Egokitek/Tinycorder/SRC/Badges.cpp

///////////////////////////////////////////////////////////
///                  TINYCORDER V2.0                    ///
///////////////////////////////////////////////////////////
///                    MAIN PROGRAM                     ///
///////////////////////////////////////////////////////////
///           Victor Barahona - July 2025               ///
///                www.victorbarahona.com               ///
///////////////////////////////////////////////////////////

#include "Badges.h"

/*
*****************************************************************************************************
***                                 HOW TO CREATE OTHER BADGES                                    ***
*** Create a jpg file with 400x240pixels. Could be made in www.canva.com with a customized canvas ***
***                                 Download the jpg file to PC.                                  ***
***              Open https://javl.github.io/image2cpp/ an insert the jpg file.                   ***
***        Follow the wizard and you will obtain the code to insert in your Tinycorder            ***
*****************************************************************************************************
*/

//Badge personal Victor Barahona asociado a www.victorbarahona.com
const unsigned char vj_personal_badge[] PROGMEM = {
  // 'Badge personal Victor Barahona, 400x240px
  0xff, 0xff, 0xff, 0xff, 0xff, 0xff, 0xff, 0xff, 0xff, 0xff, 0xff, 0xff, 0xff, 0xff, 0xff, 0xff,
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
  0xff, 0xff, 0xff, 0xff, 0xff, 0xff, 0xff, 0xff, 0xff, 0xff, 0xff, 0xff, 0xff, 0x00, 0x00, 0x3f,
  0xff, 0xff, 0xff, 0xff, 0xff, 0xff, 0xff, 0xff, 0xff, 0xfc, 0x07, 0xff, 0xff, 0xff, 0xff, 0xff,
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
};


//////////////////////
///   END OF FILE  ///
//////////////////////
