Egokitek/Tinycorder/SRC/Badges.h

///////////////////////////////////////////////////////////
///                  TINYCORDER V2.0                    ///
///////////////////////////////////////////////////////////
///                    MAIN PROGRAM                     ///
///////////////////////////////////////////////////////////
///           Victor Barahona - July 2025               ///
///                www.victorbarahona.com               ///
///////////////////////////////////////////////////////////

#ifndef BADGES_H
#define BADGES_H

#include <Arduino.h>

extern const unsigned char vj_personal_badge[];

#endif

//////////////////////
///   END OF FILE  ///
//////////////////////
